CalPolyRobotics/IGVC-boards/Hermes v1 Final/Hermes v1.brd

## EAGLE design Hermes v1 Final/Hermes v1.brd (2016-10-07)

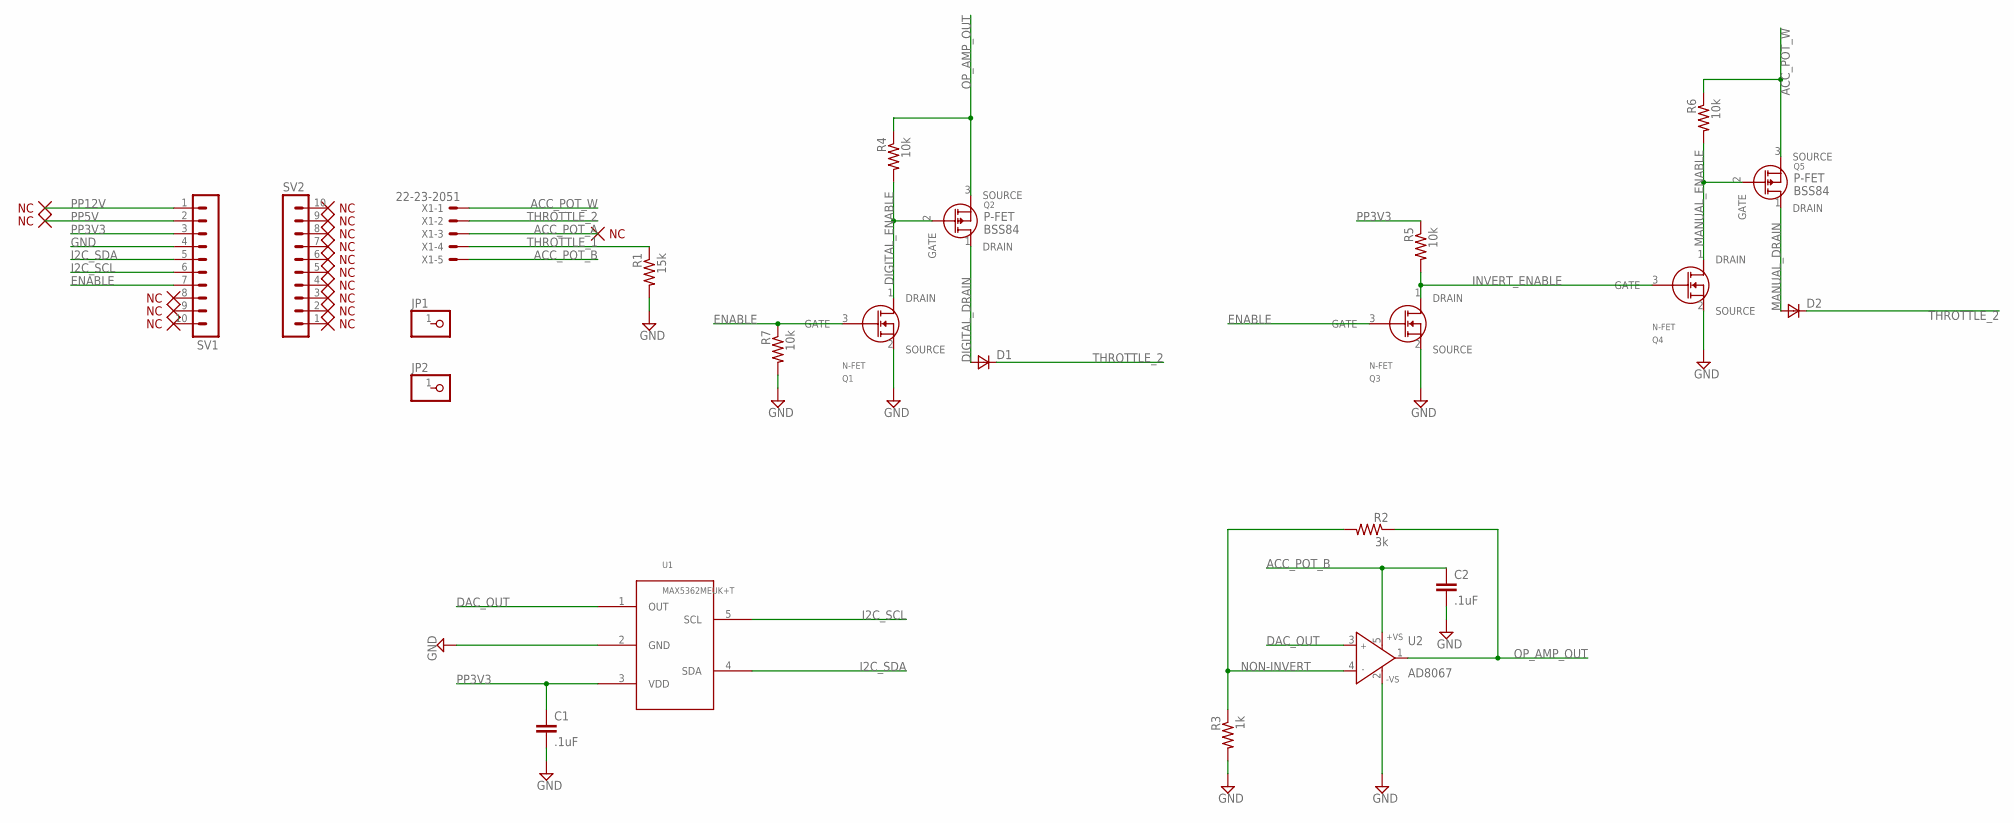
[picture p19: schematic Hermes v1.sch]

Parts:
C1, C2: .1uF; C0402
D1: DSOD323; SOD323; DIGI BAT54WS-FDICT-ND
D2: DSOD323; SOD323
JP1, JP2: PINHD-1X1; 1X01
Q1, Q3, Q4: NMOSFET; SOT-23
Q2, Q5: P-FET; SOT-23; DIGI BSS84CT-ND
R1: 15k; R0603
R2: 3k; R0603
R3: 1k; R0603
R4, R5, R6, R7: 10k; R0603
SV1, SV2: MA10-1
U1: DAC; SOT23-5
U2: AD8067; SOT23-5; DIGI 497-13051-1-ND
X1: 22-23-2051

Connections:
ACC_POT_A: X1.3
ACC_POT_B: C2.1, U2.5 (+VS), X1.5
ACC_POT_W: Q5.3 (SOURCE), R6.1, X1.1
DAC_OUT: U1.1 (OUT), U2.3 (IN+)
DIGITAL_DRAIN: D1.2 (A), Q2.1 (DRAIN)
DIGITAL_ENABLE: Q1.1 (DRAIN), Q2.2 (GATE), R4.2
ENABLE: Q1.3 (GATE), Q3.3 (GATE), R7.1, SV1.7
GND: C1.2, C2.2, Q1.2 (SOURCE), Q3.2 (SOURCE), Q4.2 (SOURCE), R1.2, R3.2, R7.2, SV1.4, U1.2 (GND), U2.2 (-VS)
I2C_SCL: SV1.6, U1.5 (SCL)
I2C_SDA: SV1.5, U1.4 (SDA)
INVERT_ENABLE: Q3.1 (DRAIN), Q4.3 (GATE), R5.2
MANUAL_DRAIN: D2.2 (A), Q5.1 (DRAIN)
MANUAL_ENABLE: Q4.1 (DRAIN), Q5.2 (GATE), R6.2
NON-INVERT: R2.2, R3.1, U2.4 (IN-)
OP_AMP_OUT: Q2.3 (SOURCE), R2.1, R4.1, U2.1 (OUT)
PP3V3: C1.1, R5.1, SV1.3, U1.3 (VDD)
PP5V: SV1.2
PP12V: SV1.1
THROTTLE_1: R1.1, X1.4
THROTTLE_2: D1.1 (C), D2.1 (C), X1.2

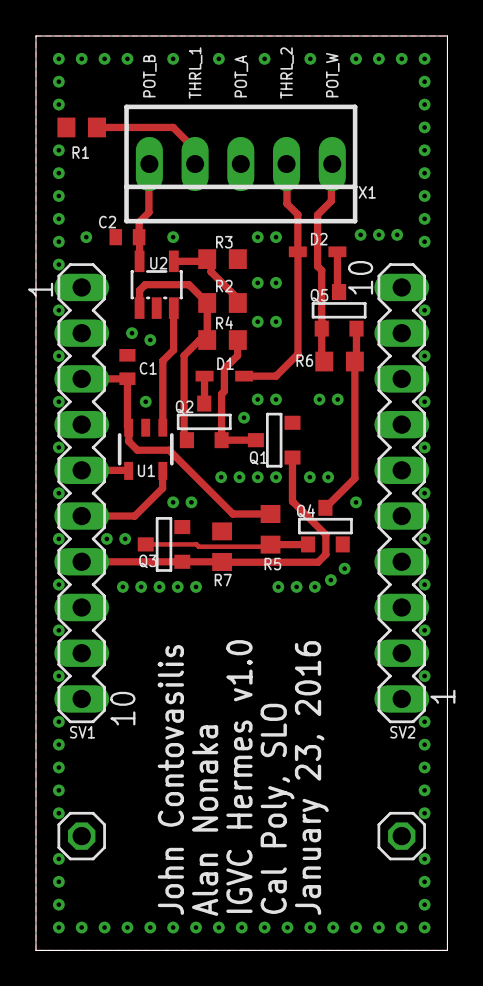
[picture p20: board Hermes v1.brd from above]

Board: 2 copper layers, 22.9 x 50.8 mm, 23 parts (0 on the bottom side), 17 nets.
